HackAveiro/vivacidade/led_board/gerber/board-B_SilkS.pdf

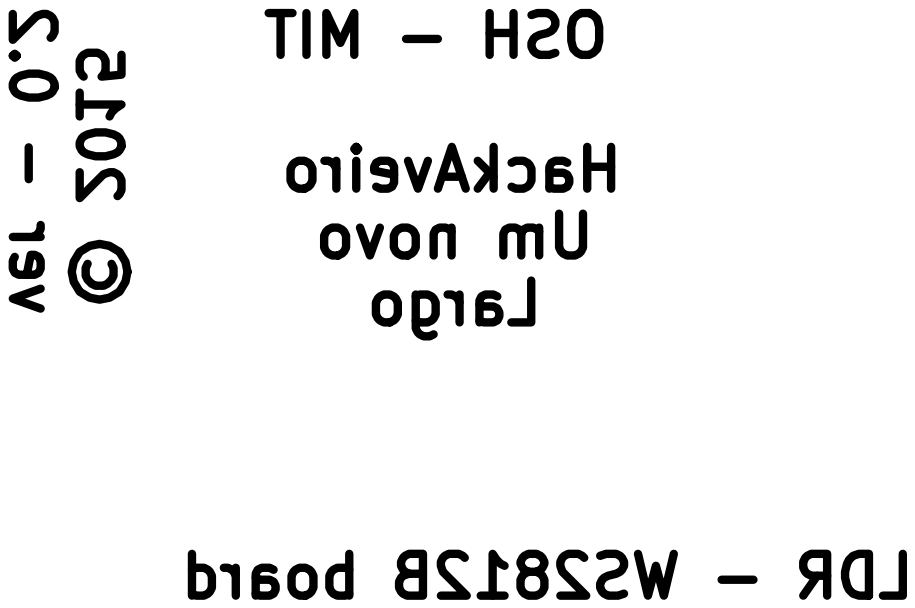
[picture p11: page 1]

LDR - WS2812B board ver - 0.2 © 2015 OSH - MIT HackAveiro
