HackAveiro/vivacidade/led_board/gerber/tiagogon/board-B_SilkS.pdf

LDR - WS2812B board ver - 0.2 © 2015 OSH - MIT HackAveiro
