HackAveiro/vivacidade/led_board/gerber/board-F_Cu.pdf

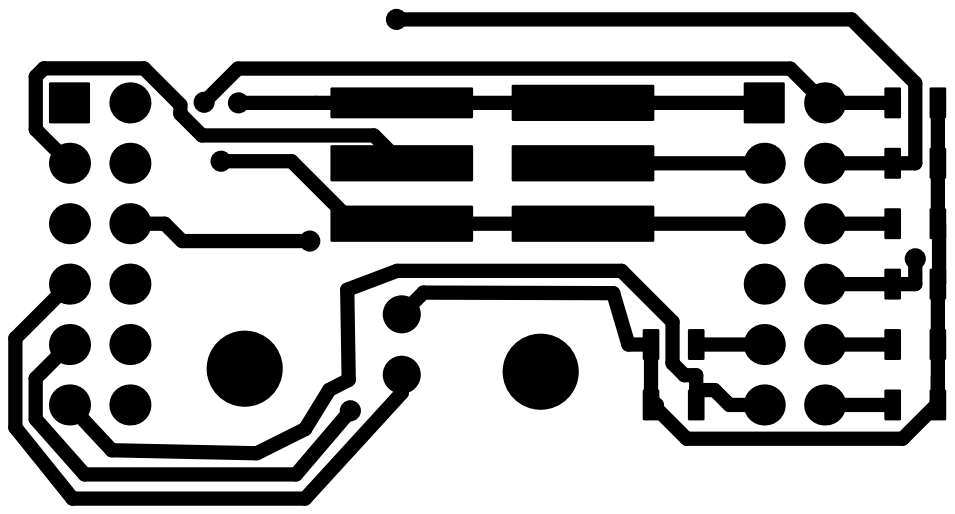
[picture p22: page 1]
