HackAveiro/vivacidade/led_board/gerber/board-F_Mask.pdf

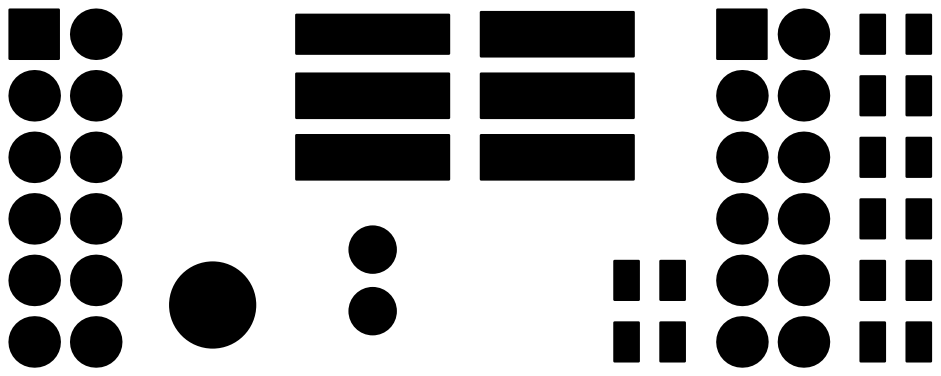
[picture p23: page 1]
