HackAveiro/vivacidade/led_board/gerber/board-F_SilkS.pdf

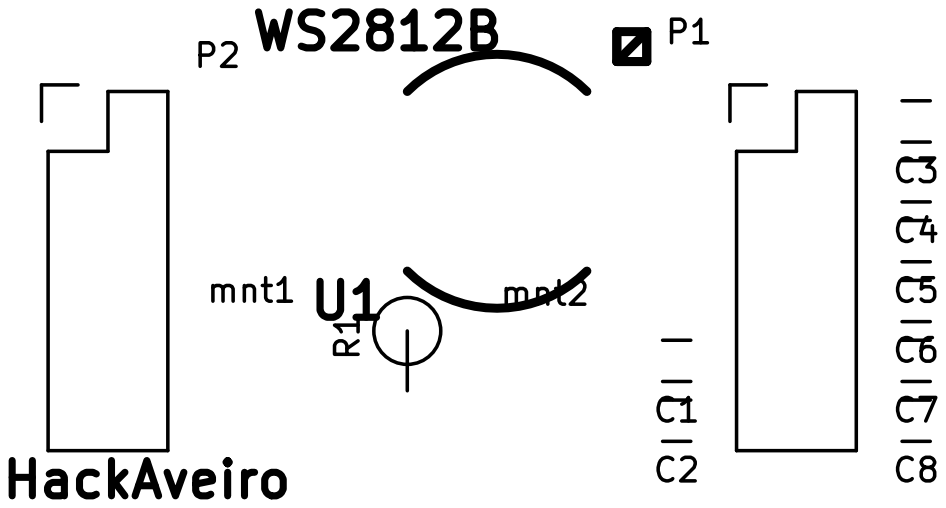
[picture p24: page 1]
